Blinkinlabs/BlinkyBall/firmware/seven_cycles_corrected.h

#define EKG_DATA_LENGTH 497
const uint8_t ekgData[EKG_DATA_LENGTH] PROGMEM = {
  0,   0,   0,   0,   0,   0,   0,   0,   1,   1, 
  2,   4,   5,   7,   9,  11,  14,  17,  20,  23, 
 27,  31,  35,  39,  44,  48,  51,  56,  60,  64, 
 67,  70,  72,  74,  76,  76,  76,  76,  75,  73, 
 71,  69,  66,  63,  60,  56,  52,  49,  45,  41, 
 37,  34,  31,  27,  24,  21,  19,  16,  14,  12, 
 10,   9,   7,   6,   5,   4,   4,   3,   3,   2, 
  2,   2,   2,   2,   3,   3,   4,   5,   6,   7, 
  9,  11,  14,  17,  20,  23,  27,  32,  36,  42, 
 47,  52,  59,  65,  71,  77,  83,  89,  95, 101, 
106, 112, 116, 118, 121, 124, 124, 124, 124, 122, 
121, 118, 116, 112, 109, 105, 100,  96,  91,  87, 
 82,  77,  73,  69,  65,  60,  56,  52,  49,  45, 
 42,  39,  36,  33,  31,  29,  27,  26,  25,  24, 
 23,  23,  23,  23,  23,  25,  26,  28,  30,  33, 
 36,  40,  44,  48,  53,  59,  65,  71,  79,  85, 
 94, 101, 109, 118, 127, 135, 144, 152, 160, 168, 
176, 182, 189, 195, 198, 202, 205, 205, 205, 205, 
203, 202, 200, 198, 195, 191, 186, 182, 177, 174, 
169, 164, 160, 153, 149, 144, 140, 135, 129, 125, 
121, 117, 113, 110, 106, 104, 101,  99,  96,  95, 
 94,  93,  91,  91,  91,  93,  94,  96,  99, 101, 
104, 108, 112, 117, 121, 127, 132, 138, 144, 150, 
158, 164, 171, 179, 186, 193, 200, 207, 214, 220, 
225, 231, 237, 241, 245, 249, 253, 253, 255, 255, 
253, 253, 249, 245, 241, 237, 231, 225, 220, 214, 
207, 200, 193, 186, 179, 171, 164, 158, 150, 144, 
138, 132, 127, 121, 117, 112, 108, 104, 101,  99, 
 96,  94,  93,  91,  91,  91,  93,  94,  95,  96, 
 99, 101, 104, 106, 110, 113, 117, 121, 125, 129, 
135, 140, 144, 149, 153, 160, 164, 169, 174, 177, 
182, 186, 191, 195, 198, 200, 202, 203, 205, 205, 
205, 205, 202, 198, 195, 189, 182, 176, 168, 160, 
152, 144, 135, 127, 118, 109, 101,  94,  85,  79, 
 71,  65,  59,  53,  48,  44,  40,  36,  33,  30, 
 28,  26,  25,  23,  23,  23,  23,  23,  24,  25, 
 26,  27,  29,  31,  33,  36,  39,  42,  45,  49, 
 52,  56,  60,  65,  69,  73,  77,  82,  87,  91, 
 96, 100, 105, 109, 112, 116, 118, 121, 122, 124, 
124, 124, 124, 121, 118, 116, 112, 106, 101,  95, 
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
