Blinkinlabs/BlinkyBall/firmware/seven_cycles.h

#define EKG_DATA_LENGTH 497
const uint8_t ekgData[EKG_DATA_LENGTH] PROGMEM = {
  0,   0,   1,   3,   5,   8,  11,  14,  18,  22, 
 27,  32,  37,  43,  48,  54,  60,  66,  72,  78, 
 83,  89,  95, 100, 106, 111, 115, 120, 124, 128, 
131, 134, 136, 138, 140, 140, 140, 140, 139, 137, 
135, 133, 130, 127, 124, 120, 116, 112, 108, 103, 
 98,  94,  89,  84,  79,  74,  70,  65,  60,  56, 
 52,  48,  44,  40,  37,  34,  32,  30,  28,  27, 
 26,  26,  26,  27,  29,  31,  34,  37,  41,  45, 
 50,  55,  60,  66,  72,  78,  84,  91,  97, 104, 
110, 116, 123, 129, 135, 141, 146, 151, 156, 161, 
165, 169, 172, 174, 176, 178, 178, 178, 178, 177, 
176, 174, 172, 169, 167, 164, 160, 157, 153, 149, 
145, 141, 137, 133, 129, 124, 120, 116, 112, 108, 
104, 100,  96,  93,  90,  87,  84,  82,  80,  79, 
 77,  77,  77,  77,  78,  80,  82,  85,  88,  92, 
 96, 101, 106, 111, 117, 123, 129, 135, 142, 148, 
155, 161, 167, 174, 180, 186, 192, 197, 202, 207, 
212, 216, 220, 223, 225, 227, 229, 229, 229, 229, 
228, 227, 226, 225, 223, 221, 218, 216, 213, 211, 
208, 205, 202, 198, 195, 192, 189, 186, 182, 179, 
176, 173, 170, 168, 165, 163, 161, 159, 157, 156, 
155, 154, 153, 153, 153, 154, 155, 157, 159, 161, 
163, 166, 169, 173, 176, 180, 184, 188, 192, 196, 
201, 205, 209, 214, 218, 222, 226, 230, 234, 237, 
240, 243, 246, 248, 250, 252, 254, 254, 255, 255, 
254, 254, 252, 250, 248, 246, 243, 240, 237, 234, 
230, 226, 222, 218, 214, 209, 205, 201, 196, 192, 
188, 184, 180, 176, 173, 169, 166, 163, 161, 159, 
157, 155, 154, 153, 153, 153, 154, 155, 156, 157, 
159, 161, 163, 165, 168, 170, 173, 176, 179, 182, 
186, 189, 192, 195, 198, 202, 205, 208, 211, 213, 
216, 218, 221, 223, 225, 226, 227, 228, 229, 229, 
229, 229, 227, 225, 223, 220, 216, 212, 207, 202, 
197, 192, 186, 180, 174, 167, 161, 155, 148, 142, 
135, 129, 123, 117, 111, 106, 101,  96,  92,  88, 
 85,  82,  80,  78,  77,  77,  77,  77,  79,  80, 
 82,  84,  87,  90,  93,  96, 100, 104, 108, 112, 
116, 120, 124, 129, 133, 137, 141, 145, 149, 153, 
157, 160, 164, 167, 169, 172, 174, 176, 177, 178, 
178, 178, 178, 176, 174, 172, 169, 165, 161, 156, 
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
