Blinkinlabs/BlinkyBall/Blink_Simulator/ekg_data.h

#ifndef EKG_DATA_H_
#define EKG_DATA_H_

#include <stdint.h>
#include <avr/pgmspace.h>

// Note: don't make this > 255!
//#define EKG_DATA_LENGTH 500
#define EKG_DATA_LENGTH 220


#define BRIGHTNESS_CORRECTED

#if defined(BRIGHTNESS_CORRECTED)

const uint8_t ekgData[EKG_DATA_LENGTH] PROGMEM = {
190, 199, 208, 217, 224, 231, 238, 243, 247, 251, 
253, 254, 255, 254, 252, 249, 246, 241, 236, 230, 
223, 217, 209, 201, 194, 185, 177, 169, 161, 154, 
146, 139, 132, 126, 120, 114, 109, 104,  99,  96, 
 92,  89,  86,  84,  82,  81,  80,  79,  79,  79, 
 79,  80,  81,  82,  84,  86,  88,  90,  93,  96, 
 99, 103, 107, 110, 115, 119, 123, 128, 133, 137, 
142, 147, 152, 157, 162, 167, 172, 177, 182, 186, 
191, 195, 199, 203, 207, 210, 213, 216, 219, 221, 
223, 224, 225, 226, 227, 227, 227, 226, 225, 224, 
222, 221, 218, 216, 213, 209, 206, 202, 198, 194, 
190, 185, 180, 175, 170, 165, 159, 154, 148, 143, 
137, 132, 126, 121, 116, 110, 105, 100,  95,  90, 
 85,  80,  76,  71,  67,  63,  59,  55,  51,  48, 
 45,  41,  38,  36,  33,  30,  28,  26,  24,  22, 
 20,  18,  16,  15,  14,  12,  11,  10,   9,   8, 
  7,   6,   6,   5,   5,   4,   4,   3,   3,   2, 
  2,   2,   1,   1,   1,   1,   1,   1,   0,   0, 
  0,   0,   0,   0,   0,   0,   0,   0,   0,   0, 
  0,   0,   0,   0,   0,   0,   0,   0,   0,   0, 
  0,   0,   0,   0,   0,   0,   0,   0,   0,   0, 
  0,   0,   0,   0,   0,   0,   0,   0,   0,   0, 
};


#else

const uint8_t ekgData[EKG_DATA_LENGTH] PROGMEM = {
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
  0,   0,   0,   0,   0,   0,   0,   0,   0,   0, 
  0,   0,   0,   0,   0,   0,   0,   0,   0,   0, 
  0,   0,   0,   0,   0,   0,   0,   0,   0,   0, 
  0,   0,   0,   0,   0,   0,   0,   0,   0,   0, 
*/
};
#endif  // BRIGHTNESS_CORRECTED

#endif  //EKG_DATA_H
